technobly/vectrex-sao/code/mplabx-pic16f886/2022-vectrex-sao.X/config.h

/* 
 * File:   config.h
 * Author: Brett Walach
 *
 * Created on October 3, 2022, 2:50 PM
 */

#ifndef CONFIG_H
#define	CONFIG_H

#include <xc.h>

#ifdef	__cplusplus
extern "C" {
#endif

// CONFIG1
#pragma config FOSC = INTRC_CLKOUT// Oscillator Selection bits (INTOSC oscillator: CLKOUT function on RA6/OSC2/CLKOUT pin, I/O function on RA7/OSC1/CLKIN)
#pragma config WDTE = OFF       // Watchdog Timer Enable bit (WDT disabled and can be enabled by SWDTEN bit of the WDTCON register)
#pragma config PWRTE = OFF      // Power-up Timer Enable bit (PWRT disabled)
#pragma config MCLRE = ON       // RE3/MCLR pin function select bit (RE3/MCLR pin function is MCLR)
#pragma config CP = OFF         // Code Protection bit (Program memory code protection is disabled)
#pragma config CPD = OFF        // Data Code Protection bit (Data memory code protection is disabled)
#pragma config BOREN = ON      // Brown Out Reset Selection bits (BOR enabled)
#pragma config IESO = ON        // Internal External Switchover bit (Internal/External Switchover mode is enabled)
#pragma config FCMEN = ON       // Fail-Safe Clock Monitor Enabled bit (Fail-Safe Clock Monitor is enabled)
#pragma config LVP = OFF        // Low Voltage Programming Enable bit (RB3 pin has digital I/O, HV on MCLR must be used for programming)

// CONFIG2
#pragma config BOR4V = BOR21V   // Brown-out Reset Selection bit (Brown-out Reset set to 2.1V)
#pragma config WRT = OFF        // Flash Program Memory Self Write Enable bits (Write protection off)

// #pragma config statements should precede project file includes.
// Use project enums instead of #define for ON and OFF.

#define _XTAL_FREQ 4000000
    
#define delay(ms)   __delay_ms(ms)

#define SOUND_ENABLED (1) // 0 to disable (or just unsolder the SOUND jumper on the PCB)

#ifdef	__cplusplus
}
#endif

#endif	/* CONFIG_H */
