technobly/vectrex-sao/code/mplabx-pic16f886/2022-vectrex-sao.X/notes.h

/* 
 * File:   notes.h
 * Author: brett
 *
 * Created on October 5, 2022, 9:35 PM
 */

#ifndef NOTES_H
#define	NOTES_H

#ifdef	__cplusplus
extern "C" {
#endif

#define A3  220
#define AS3 233
#define B3  247
    
#define C4  262
#define CS4 277
#define D4  294
#define DS4 311
#define E4  330
#define F4  350
#define FS4 370
#define G4  392
#define GS4 415
#define A4  440
#define AS4 466
#define B4  494

#define C5  523
#define CS5 554
#define D5  587
#define DS5 622
#define E5  660
#define F5  698
#define FS5 740
#define G5  784
#define GS5 831
#define A5  880
#define AS5 932
#define B5  988

#define C6  1046
#define CS6 1109
#define D6  1175
#define DS6 1245
#define E6  1319
#define F6  1397
#define FS6 1480
#define G6  1568
#define GS6 1661
#define A6  1760
#define AS6 1865
#define B6  1976

uint16_t notes[] = {
    262,
    277,
    294,
    311,
    330,
    350,
    370,
    392,
    415,
    440,
    466,
    494,
    523,
    554,
    587,
    622,
    660,
    698,
    740,
    784,
    831,
    880,
    932,
    988,
    1046,
    1109,
    1175,
    1245,
    1319,
    1397,
    1480,
    1568,
    1661,
    1760,
    1865,
    1976
};


#ifdef	__cplusplus
}
#endif

#endif	/* NOTES_H */
